christopherwj/SDG3/allAboutcircuits/Class_D_Amplifier_prototype_SDG3.pdf

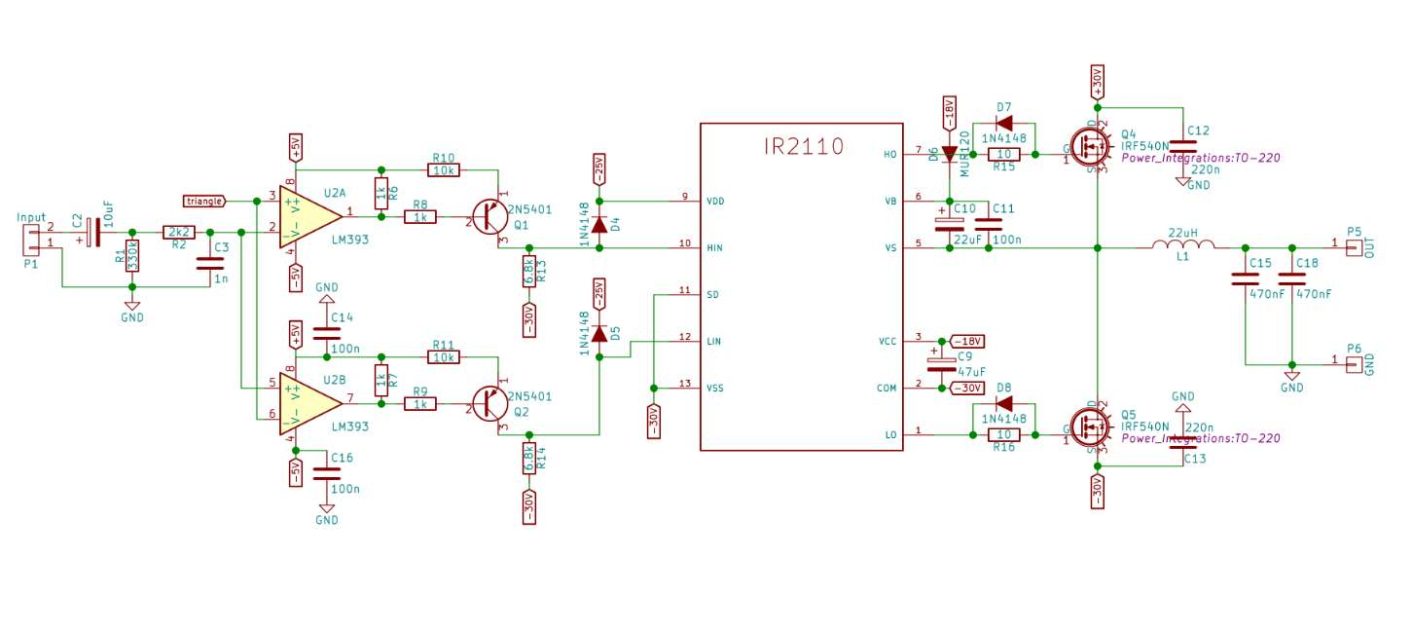
[picture p1: figure]
