christopherwj/SDG3/Photos/Block Diagram of a Class-D Amplifier.png

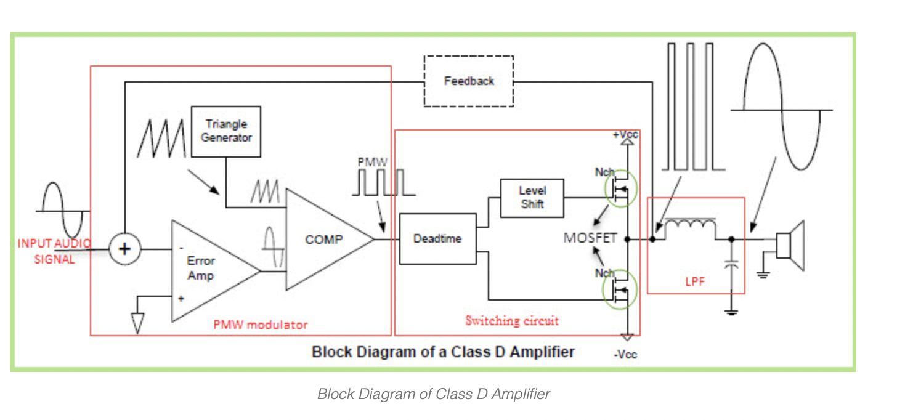
Photos/Block Diagram of a Class-D Amplifier.png
