christopherwj/SDG3/Photos/OPAMP_carrier_signal.png

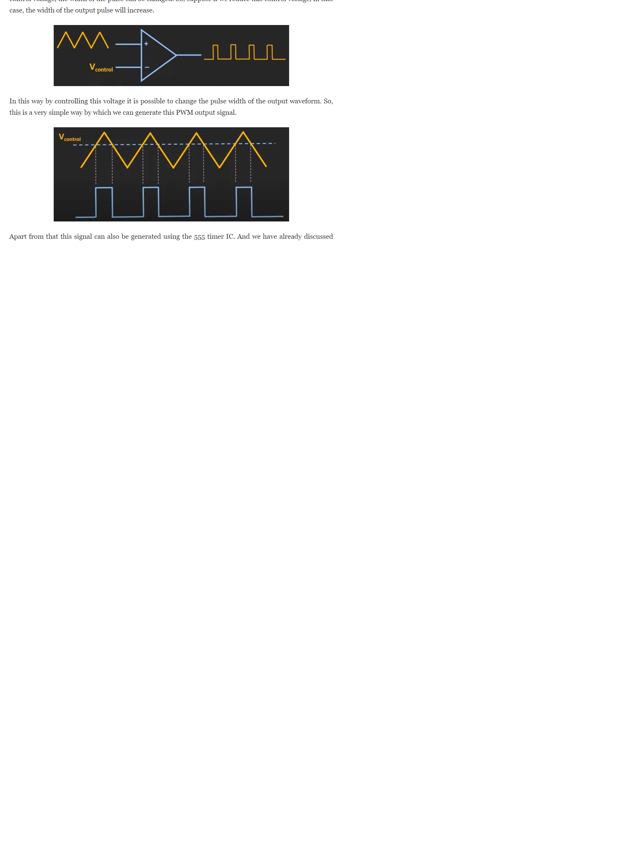
Photos/OPAMP_carrier_signal.png
