christopherwj/SDG3/Photos/Oscilloscope Captures/12V 5V Circuit/Comparator/outComparator.bmp

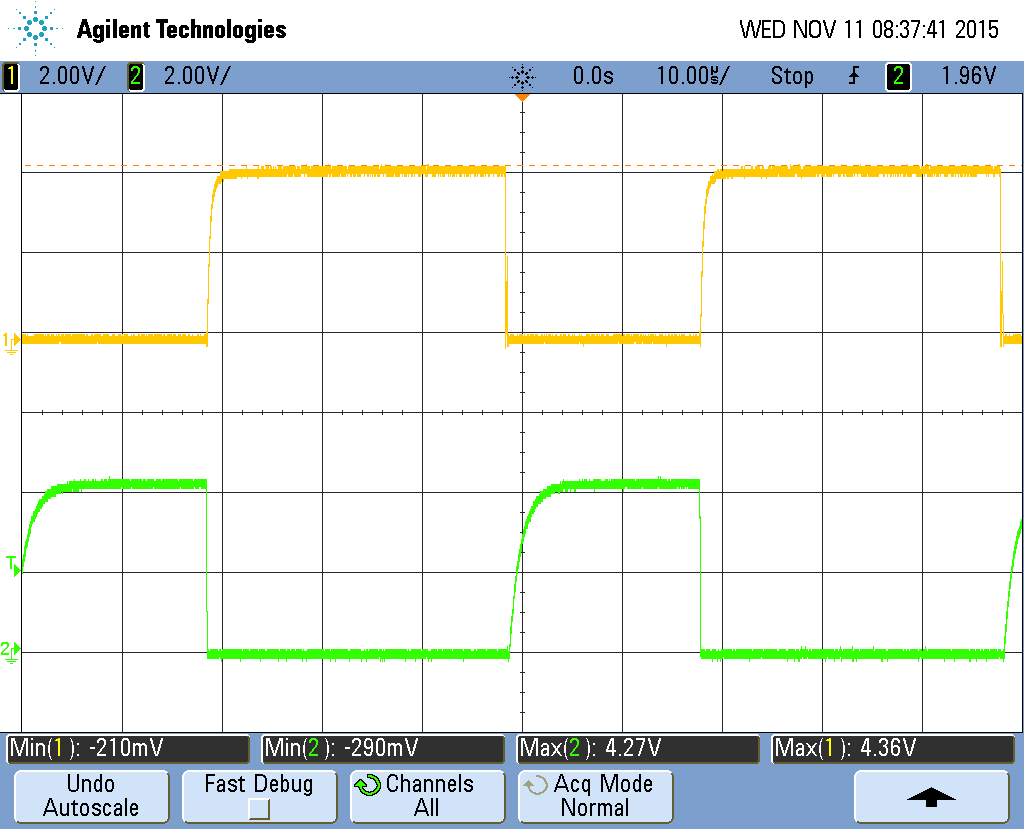
Photos/Oscilloscope Captures/12V 5V Circuit/Comparator/outComparator.bmp
