christopherwj/SDG3/Photos/Oscilloscope Captures/12V 5V Circuit/Gate Driver/LinvsHin.bmp

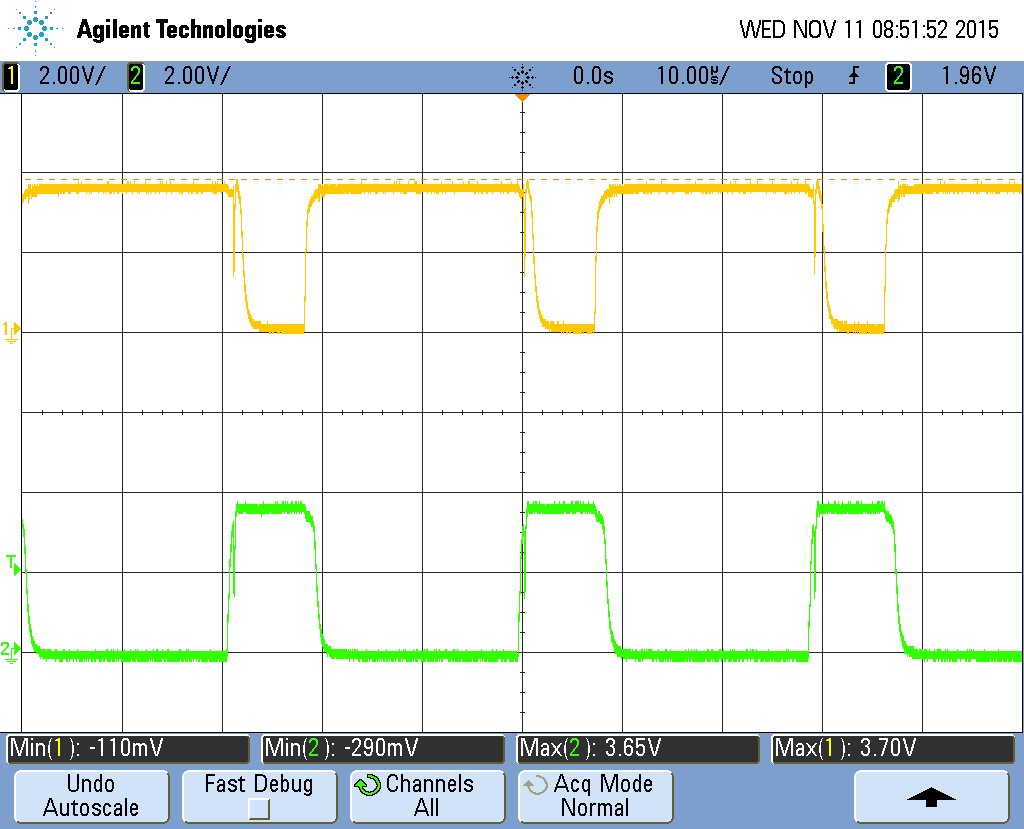
Photos/Oscilloscope Captures/12V 5V Circuit/Gate Driver/LinvsHin.bmp
