christopherwj/SDG3/Photos/Oscilloscope Captures/12V 5V Circuit/Gate Driver/LinvsLout.bmp

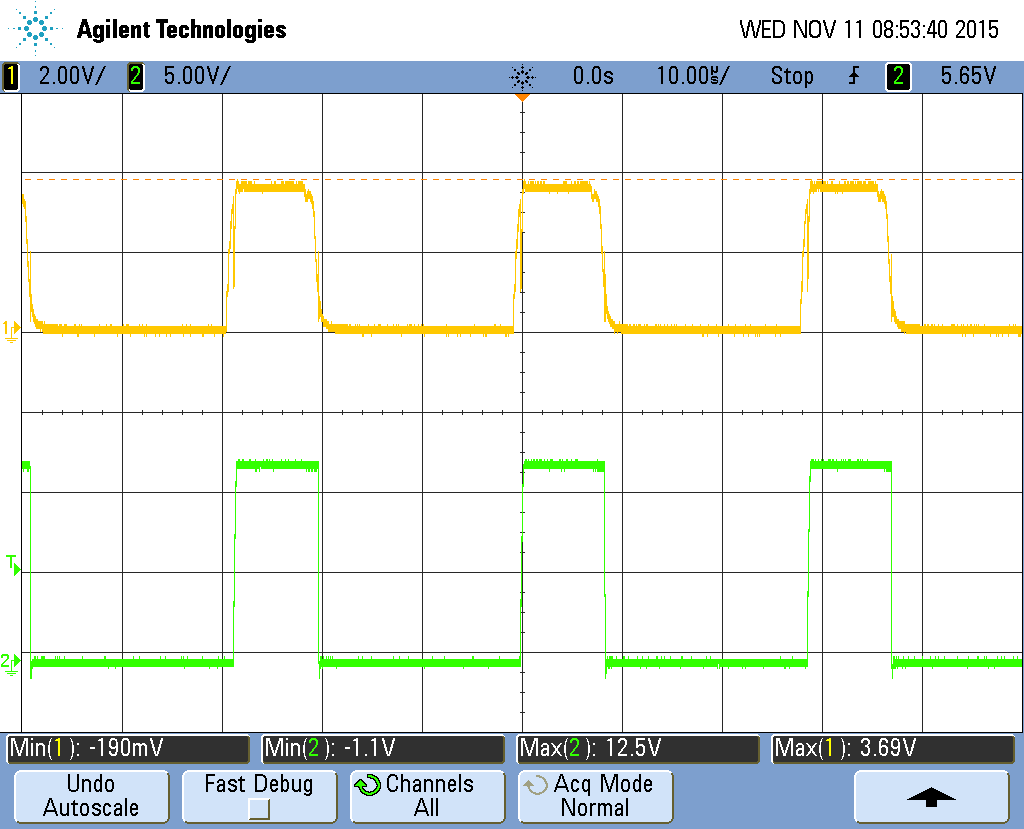
Photos/Oscilloscope Captures/12V 5V Circuit/Gate Driver/LinvsLout.bmp
