christopherwj/SDG3/Photos/Oscilloscope Captures/12V 5V Circuit/Input and Output Signals/555vsBT.bmp

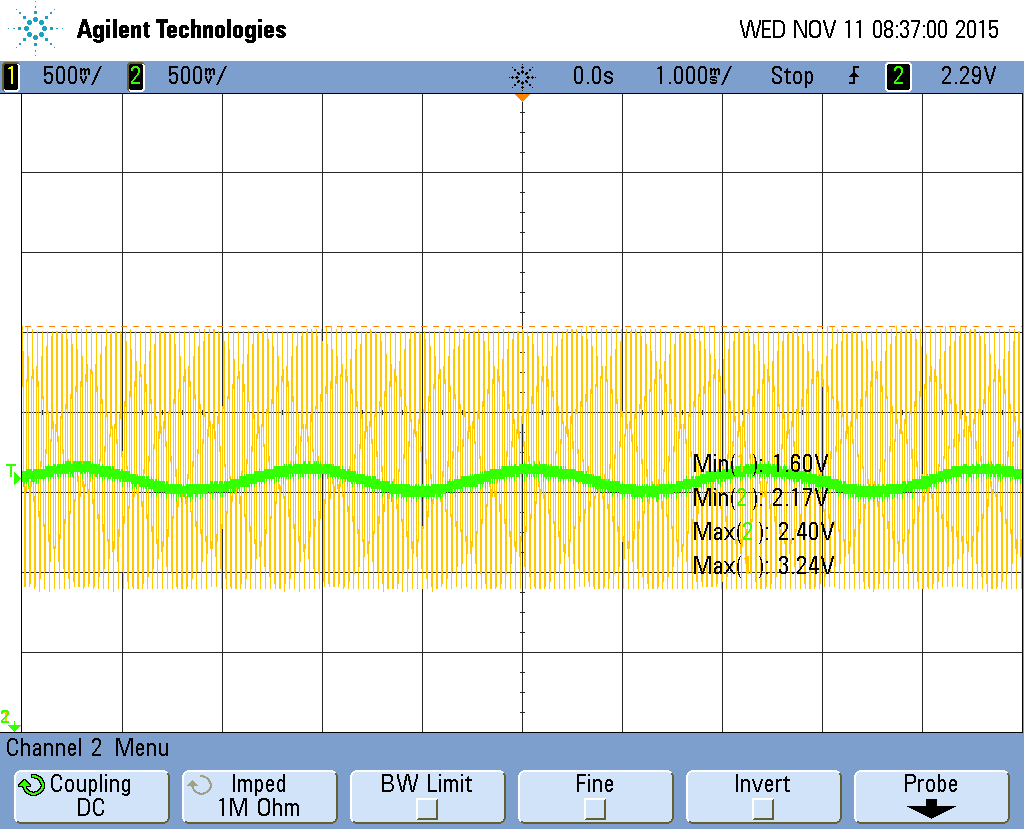
Photos/Oscilloscope Captures/12V 5V Circuit/Input and Output Signals/555vsBT.bmp
