christopherwj/SDG3/Photos/Oscilloscope Captures/12V 5V Circuit/Input and Output Signals/OutsideInductorInsideInductor.bmp

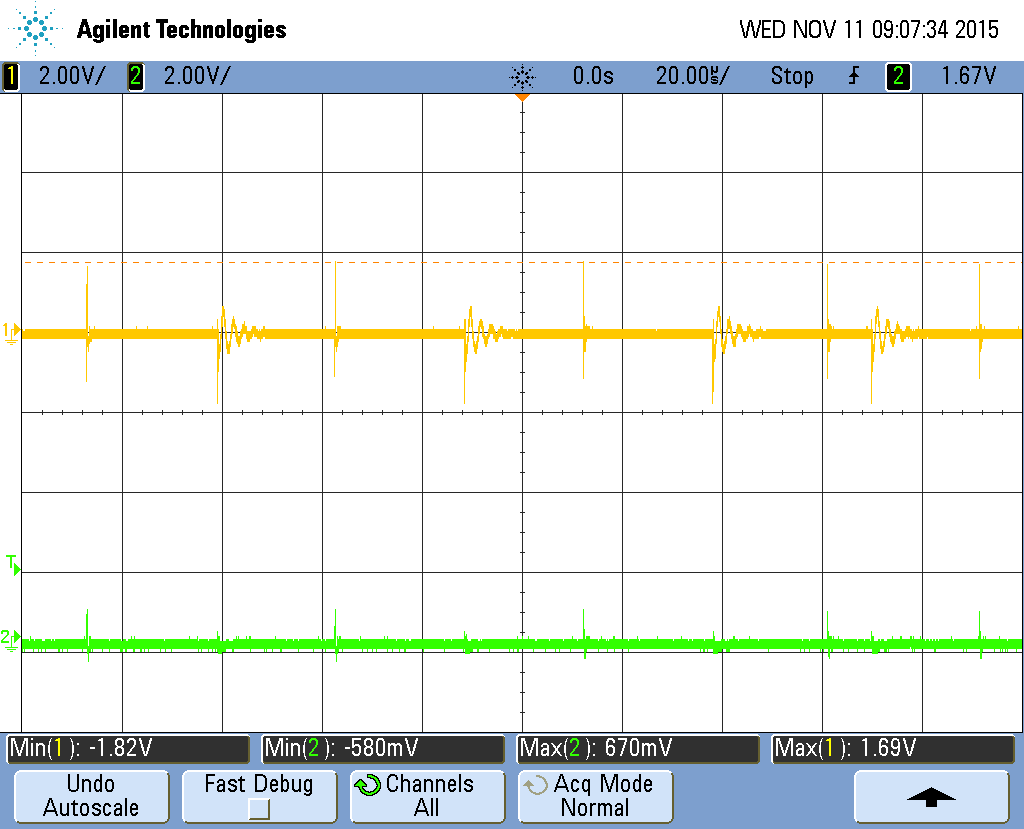
Photos/Oscilloscope Captures/12V 5V Circuit/Input and Output Signals/OutsideInductorInsideInductor.bmp
