christopherwj/SDG3/Photos/Oscilloscope Captures/Class-D Oscope 2021 Nov 8/Labled Images/gate_driver_iput_HIN_DMM.png

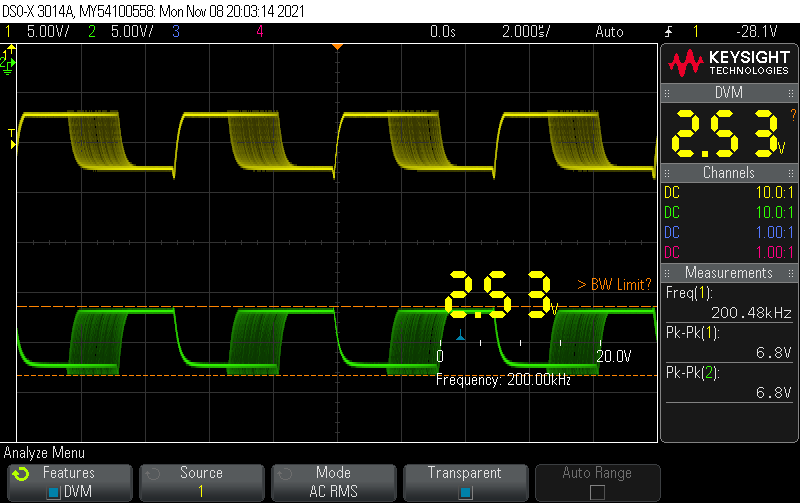
Photos/Oscilloscope Captures/Class-D Oscope 2021 Nov 8/Labled Images/gate_driver_iput_HIN_DMM.png
