christopherwj/SDG3/Photos/Oscilloscope Captures/Class-D Oscope 2021 Nov 8/Nonlabeled Images/scope_4.png

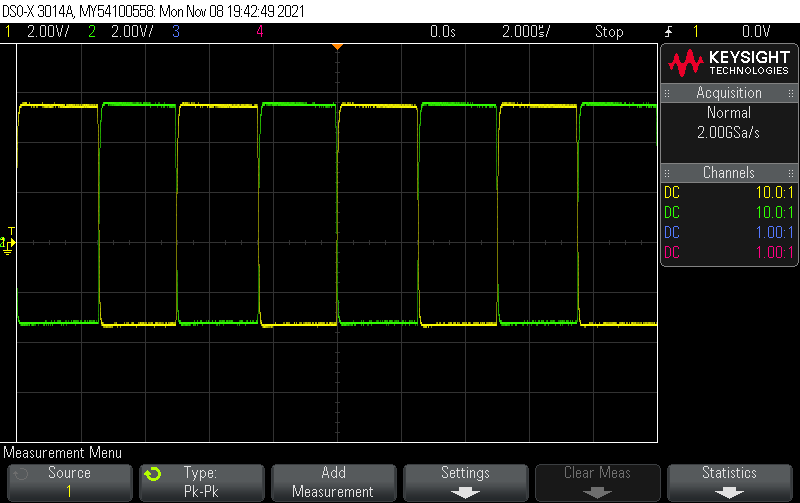
Photos/Oscilloscope Captures/Class-D Oscope 2021 Nov 8/Nonlabeled Images/scope_4.png
