christopherwj/SDG3/Photos/PWM_3L.gif

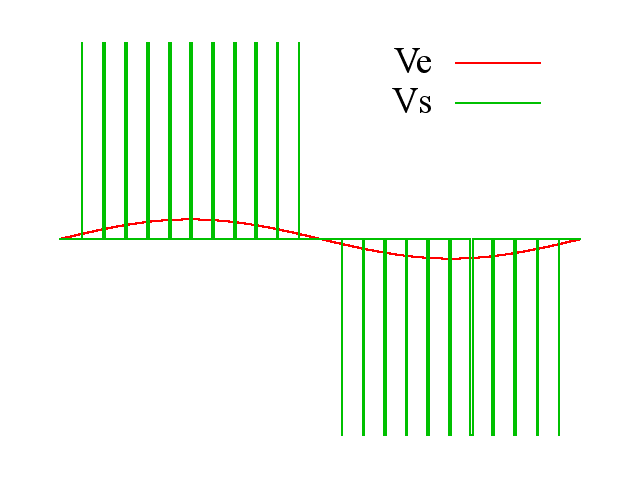
Photos/PWM_3L.gif
