christopherwj/SDG3/schematics/555_timer/general_schematic.png

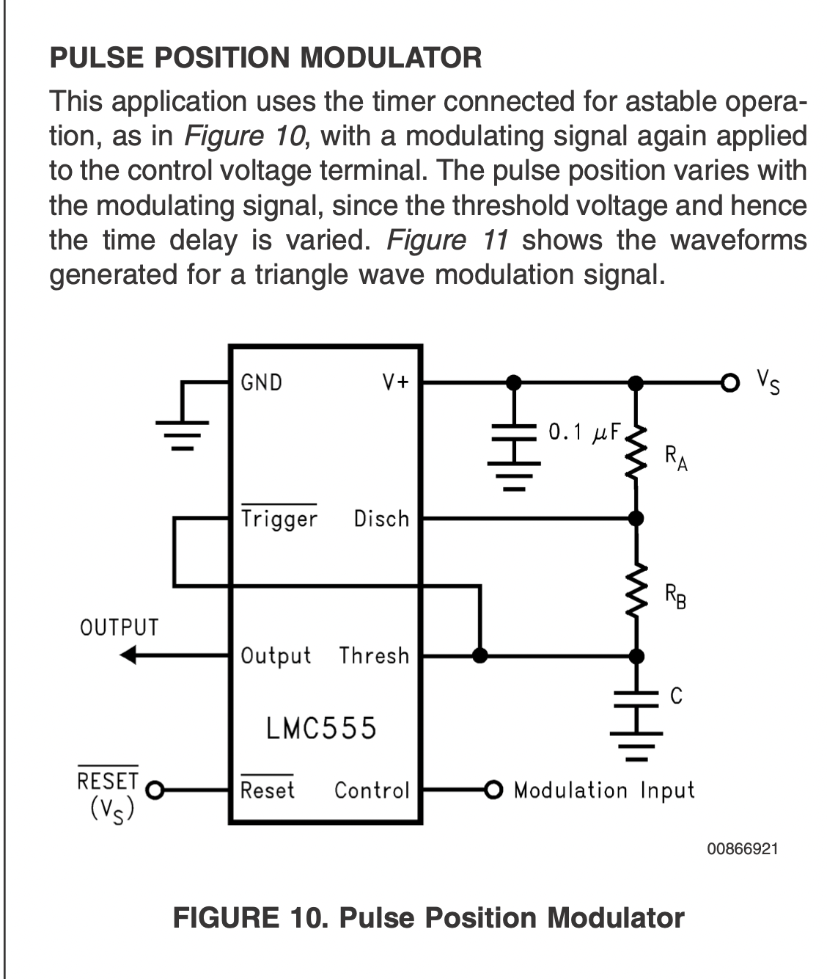
schematics/555_timer/general_schematic.png
