christopherwj/SDG3/Simulations/Senior Design A/Comparator/Comparator Circuit Schematic.PNG

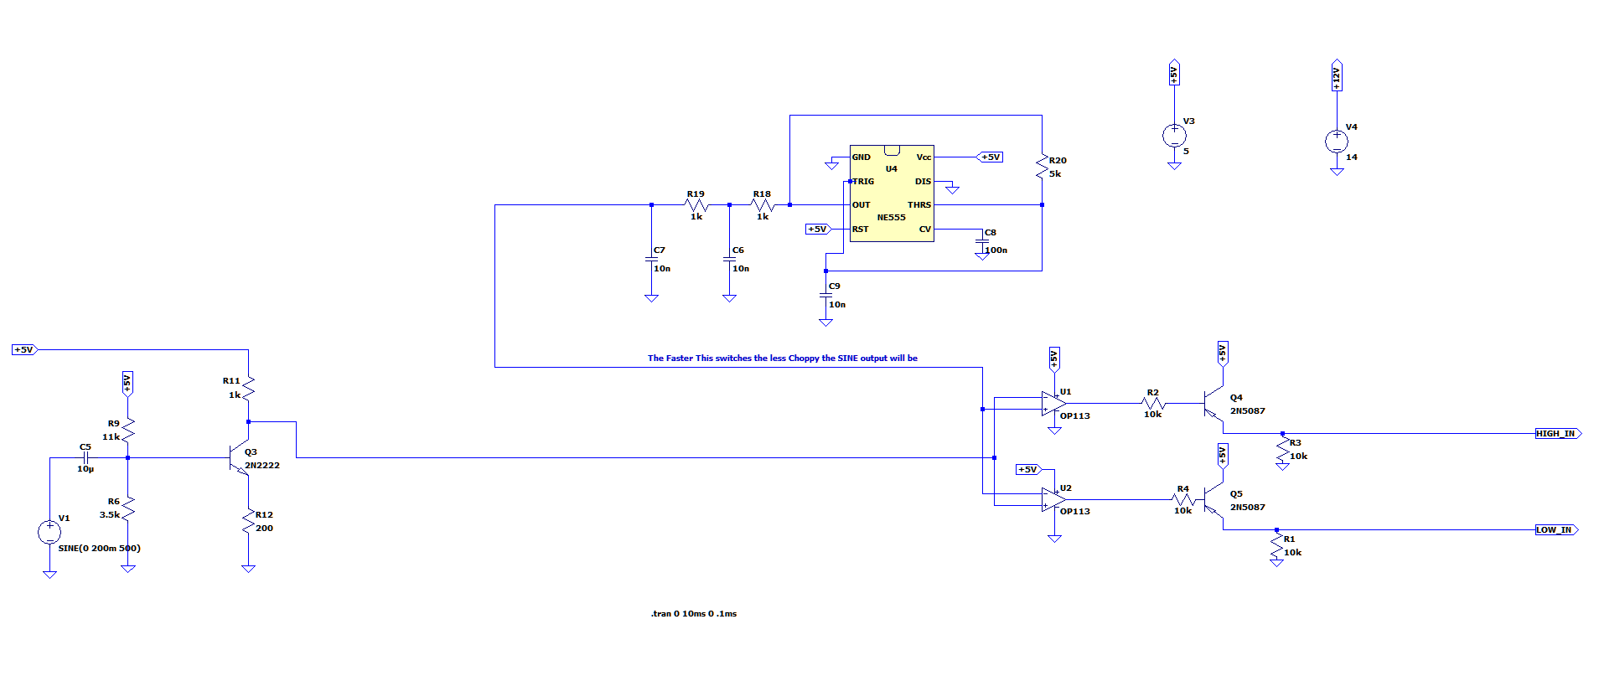
Simulations/Senior Design A/Comparator/Comparator Circuit Schematic.PNG
