christopherwj/SDG3/Simulations/Senior Design A/LowPassRC20kHz.png

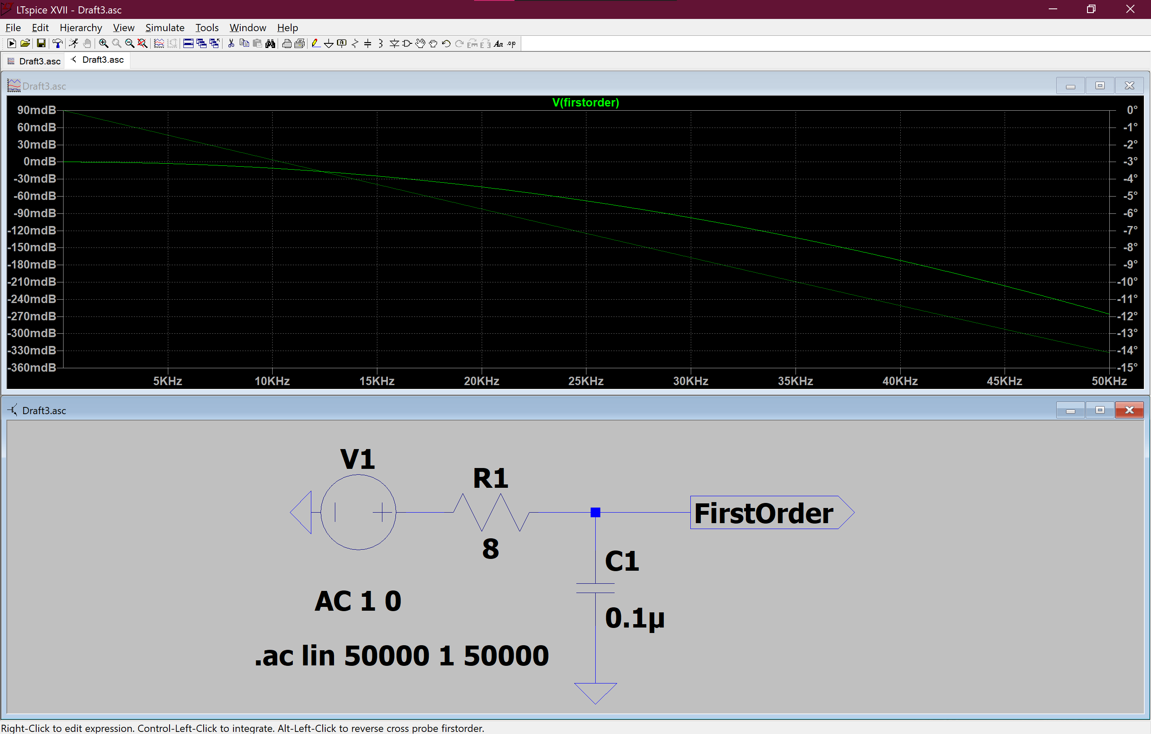
Simulations/Senior Design A/LowPassRC20kHz.png
