christopherwj/SDG3/Simulations/Senior Design A/Simulation Outputs/HinvsHout.PNG

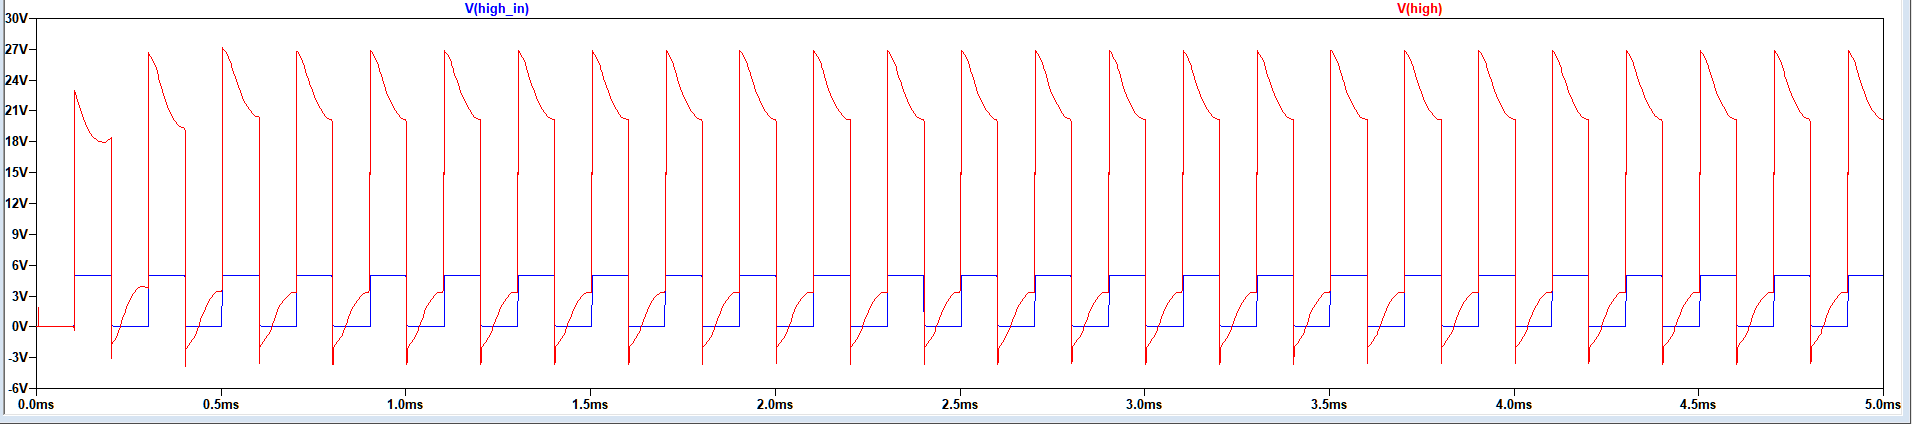
Simulations/Senior Design A/Simulation Outputs/HinvsHout.PNG
