christopherwj/SDG3/Hardware/Component Datasheets/NE555P Timer/pin_out_datasheet.png

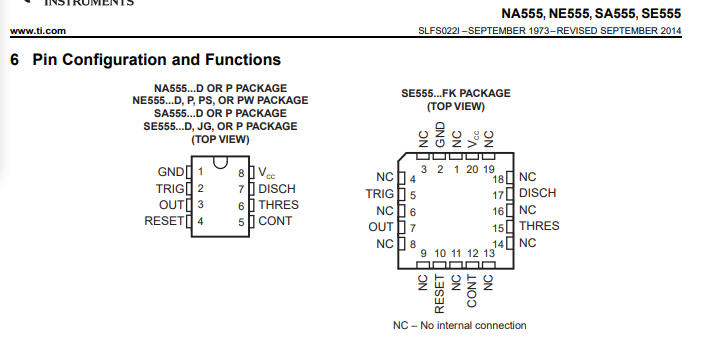
Hardware/Component Datasheets/NE555P Timer/pin_out_datasheet.png
