christopherwj/SDG3/schematics/555_timer/component_values.png

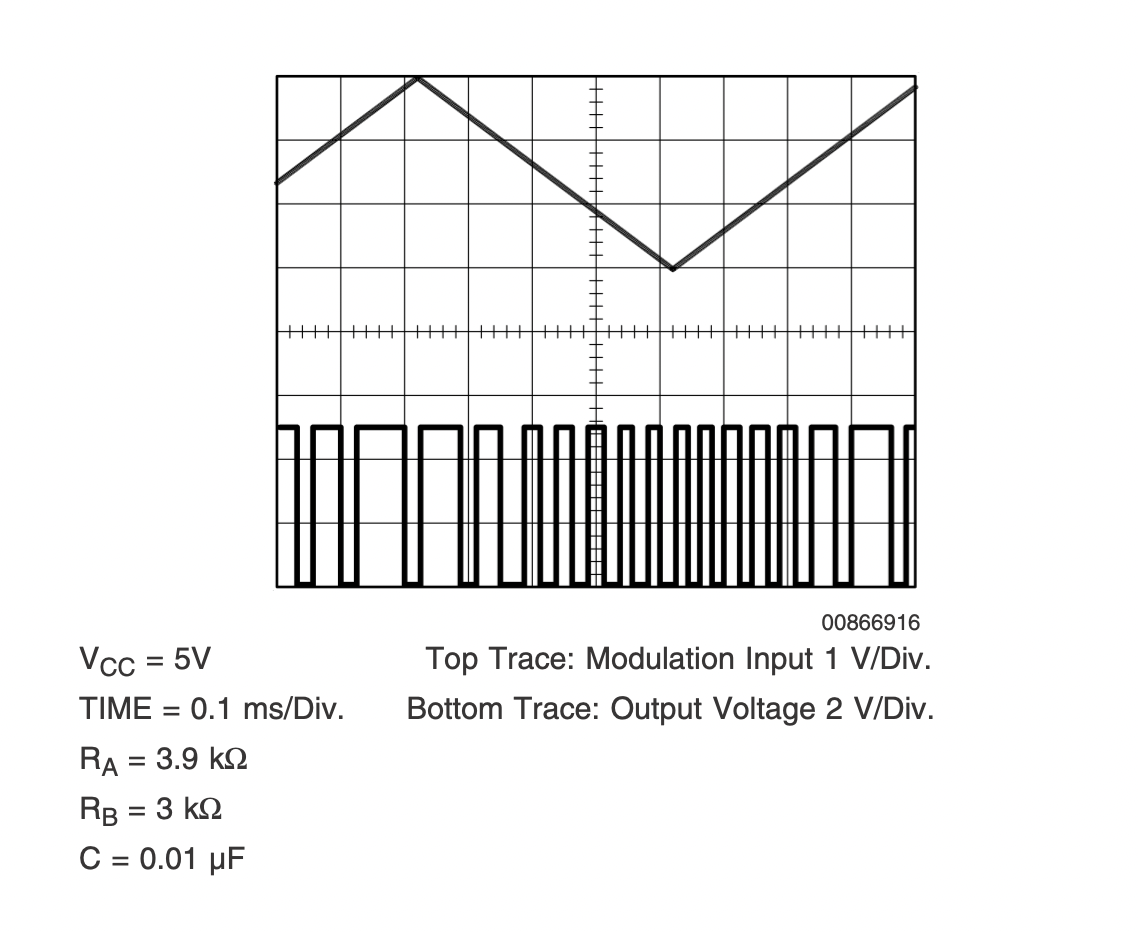
schematics/555_timer/component_values.png
