christopherwj/SDG3/Simulations/Simulation Components/PSpice Models/IR2011 Gate Driver/Model/results/demo_testbench.png

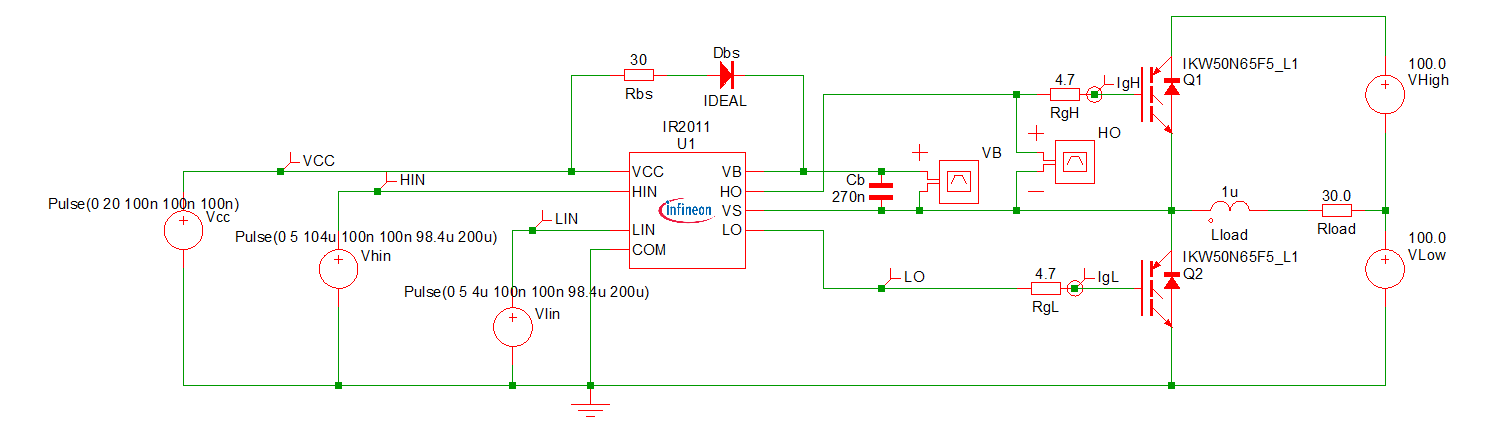
Simulations/Simulation Components/PSpice Models/IR2011 Gate Driver/Model/results/demo_testbench.png
