christopherwj/SDG3/Simulations/Simulation Components/PSpice Models/IR2011 Gate Driver/Model/results/waveforms.png

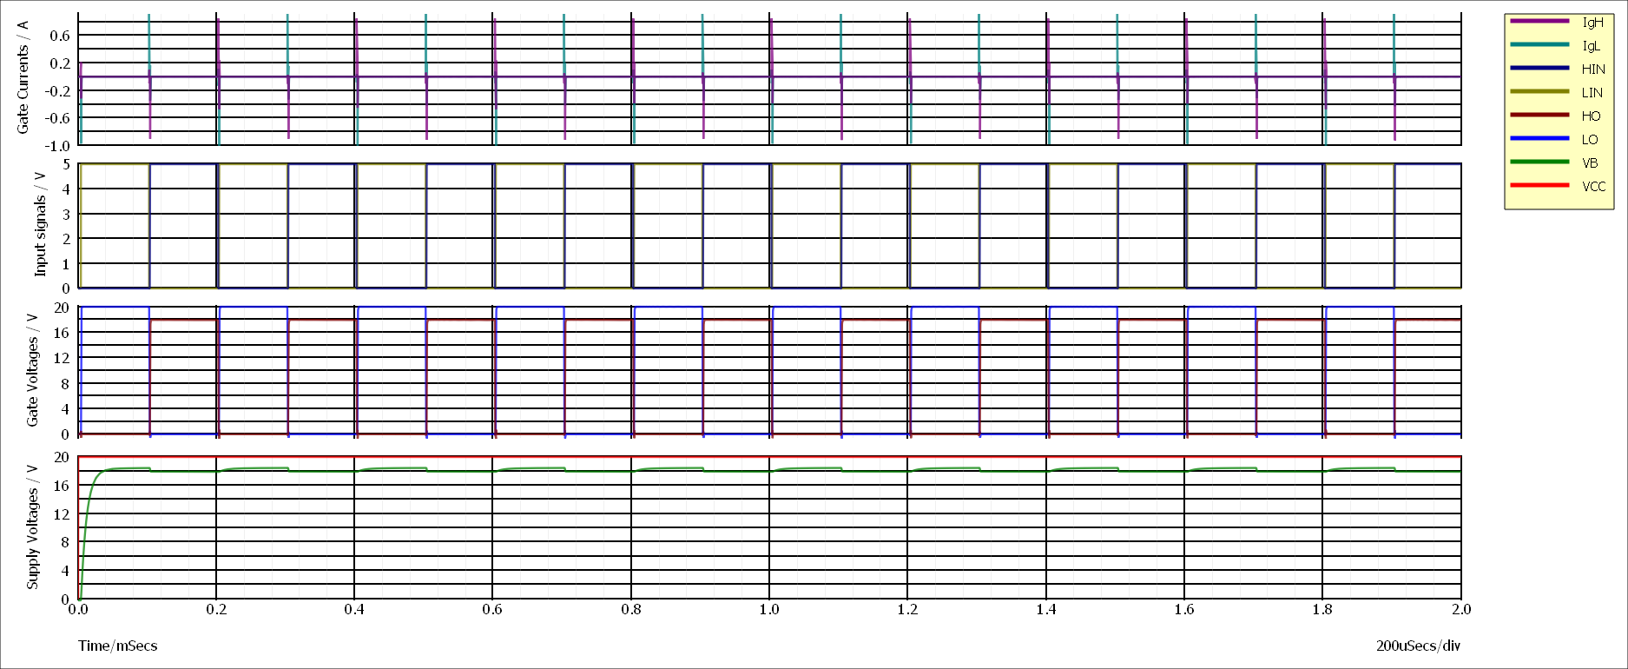
Simulations/Simulation Components/PSpice Models/IR2011 Gate Driver/Model/results/waveforms.png
