christopherwj/SDG3/allAboutcircuits/Copper.pdf

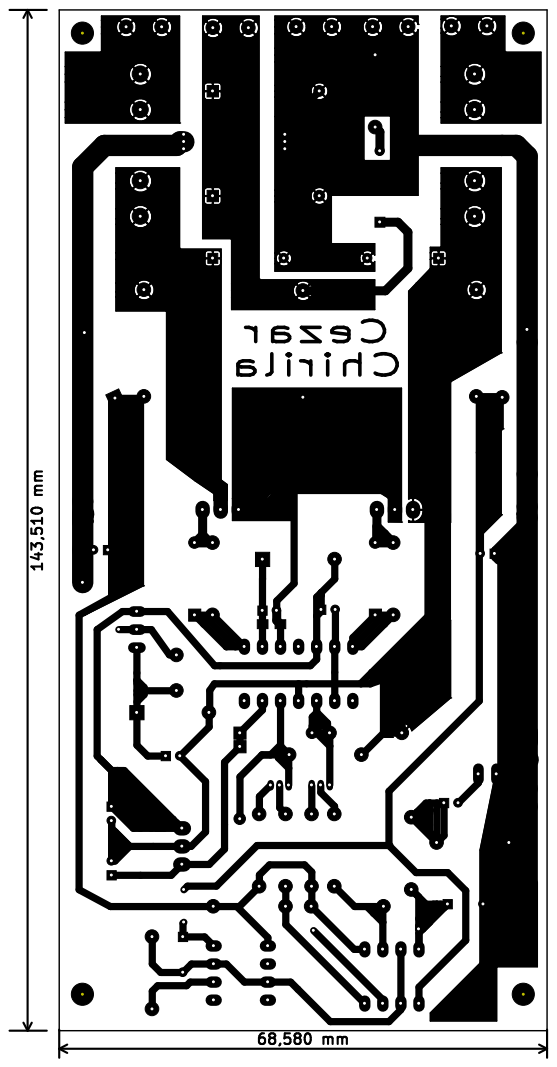
[picture p48: page 1]
