christopherwj/SDG3/allAboutcircuits/Silk.pdf

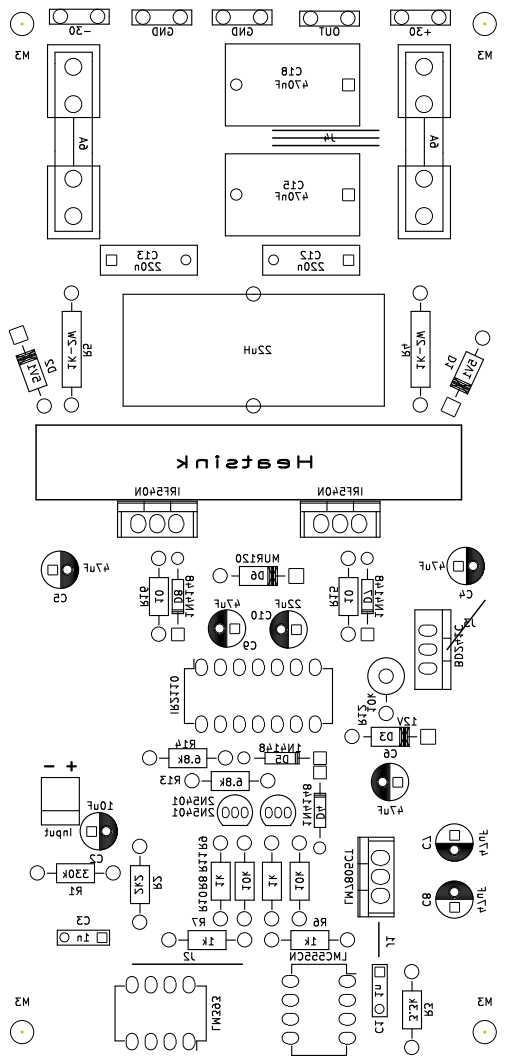
[picture p49: page 1]
