christopherwj/SDG3/Simulations/Senior Design A/LowPassRC20kHz.asc

C1: cap; 0.1µ
R1: res; 8
V1: voltage; ""; AC 1 0
Named nets: 0, FirstOrder
.ac lin 50000 1 50000
