christopherwj/SDG3/Simulations/Senior Design A/CompleteCircuit.asc

C4: cap; 10µ
C5: cap; 10n
C6: cap; 10n
C7: cap; 100n
C8: cap; 10n
C9: cap; 60µ
C10: cap; 270n
D2: diode; 1N914
L2: ind; 500µ
M3: nmos; IRF510
M4: nmos; IRF510
Q1: npn; 2N2222
Q2: pnp; 2N5087
Q3: pnp; 2N5087
R4: res; 3.5k
R5: res; 11k
R6: res; 1k
R7: res; 200
R8: res; 1k
R9: res; 1k
R10: res; 5k
R11: res; 10k
R12: res; 10k
R13: res; 10k
R14: res; 10k
R15: res; 4.7
R16: res; 4.7
R17: res; 4
U1: IR2113
U2: NE555
U3: OP113
U4: OP113
V3: voltage; SINE(0 200m 500)
V4: voltage; 5
V6: voltage; 14
V8: voltage; 14
Named nets: HIN, LIN, 0, +5V, +12V, Load, HIGH, LOW
.tran 0 5ms 1ms
The Faster This switches the less Choppy the SINE output will be
