christopherwj/SDG3/Simulations/Senior Design A/Comparator and 555 Timer Circuits/555Timerdraft.asc

C1: cap; .01µ
C2: cap; 0.1µ
R1: res; 10k
R2: res; 6k
R3: res; 1k
U1: NE555
V1: voltage; 5
Named nets: PulseOutput, 0, TriangleWave
.tran 10ms
