christopherwj/SDG3/Simulations/Senior Design A/Gate Driver Circuit 1/2113GateDriver.asc

C1: cap; 66µ
C2: cap; 10n
D1: diode; 1N914
D2: diode; 1N914
D3: diode; 1N914
L1: ind; 33µ
M1: nmos; IRF510
M2: nmos; IRF510
R1: res; 10
R2: res; 10
R3: res; 4; pwr=100
U1: IR2113
V1: voltage; 12
V2: voltage; PULSE(0 5 104u 100n 100n 98.4u 200u)
V3: voltage; PULSE(0 5 4u 100n 100n 98.4u 200u)
V4: voltage; 5
V8: voltage; 12
Named nets: 0, Load, HIGH, LOW, HIGH_IN, LOW_IN
.tran 0 5ms 0 .5ms
