christopherwj/SDG3/Simulations/Senior Design A/Comparator and 555 Timer Circuits/comparatorCircuit_draft.asc

C5: cap; 10µ
C6: cap; 10n
C7: cap; 10n
C8: cap; 100n
C9: cap; 10n
Q3: npn; 2N2222
Q4: pnp; 2N5087
Q5: pnp; 2N5087
R1: res; 10k
R2: res; 10k
R3: res; 10k
R4: res; 10k
R6: res; 3.5k
R9: res; 11k
R11: res; 1k
R12: res; 200
R18: res; 1k
R19: res; 1k
R20: res; 5k
U1: OP113
U2: OP113
U4: NE555
V1: voltage; SINE(0 200m 500)
V3: voltage; 5
V4: voltage; 14
Named nets: 0, +5V, +12V, LOW_IN, HIGH_IN
.tran 0 10ms 0 .1ms
The Faster This switches the less Choppy the SINE output will be
