christopherwj/SDG3/Simulations/Senior Design A/Comparator/comparatorCircuit_draft.asc

C1: cap; 10µ
C2: cap; 1n
C3: cap; 100n
C4: cap; 100n
R1: res; 330k
R2: res; 2200
R3: res; 1000
R4: res; 1000
R5: res; 10k
R6: res; 1000
R7: res; 10k
R8: res; 1000
U1: LT1018
U2: LT1018
U3: LM339
U4: LM339
Named nets: 0, +5V, -5V
