christopherwj/SDG3/Simulations/GateDriver/GateDriverworking.asc

C1: cap; 1µ
C2: cap; 270n
D1: diode; 1N914
L1: ind; 36µ
M1: nmos; IRF510
M2: nmos; IRF510
R1: res; 12
R2: res; 12
R3: res; 4; pwr=20
U3: IR2113
V1: voltage; 12
V2: voltage; PULSE(1 5 104u 100n 100n 98.4u 200u)
V3: voltage; PULSE(1 5 4u 100n 100n 98.4u 200u)
V4: voltage; 12
Named nets: 0, Load, HIGH, LOW, HIGH_IN, LOW_IN, 12v, 5v
.tran 0 5ms 0 .5ms
