christopherwj/SDG3/Simulations/LevelShifter/LevelShifter.asc

M1: nmos; IRF510
R1: res; 10k
R2: res; 10k
V1: voltage; PULSE(0 3.3 1 0 0 1 5)
V2: voltage; 5
V3: voltage; 3.3
Named nets: 0
.tran 20
